rascafr/esp32-din-cctv/src/secrets.h

#ifndef SECRETS
#define SECRETS

/*
 * Telegram API credentials
 * Find how yo generate your bot token here: https://core.telegram.org/api#bot-api
 */
#define BOT_TOKEN "1234567890:ABCDEF"
#define CHAT_ID "1234567890"

/*
 * WiFi configuration
 */
#define WIFI_SSID "Your Hotspot 📡"
#define WIFI_PASSWORD "1234567890"

#endif
